MAWoodMain/esp-powermonitor/main/wifi.c

//
// Created by MattWood on 21/07/2021.
//

/**************************** LIB INCLUDES ******************************/
/**************************** USER INCLUDES *****************************/
#include "wifi.h"
#include "esp_wifi.h"
#include "esp_event.h"
#include "config.h"
/******************************* DEFINES ********************************/
#define WIFI_CONNECTED_BIT BIT0
#define WIFI_FAIL_BIT      BIT1
/***************************** STRUCTURES *******************************/
/************************** FUNCTION PROTOTYPES *************************/
static void wifi_event_handler(void* arg, esp_event_base_t event_base,
                               int32_t event_id, void* event_data);
/******************************* CONSTANTS ******************************/
static const char *TAG = "WIFI";
/******************************* VARIABLES ******************************/
static EventGroupHandle_t wifi_event_group;
static int wifi_retry_num = 0;
/*************************** PUBLIC FUNCTIONS ***************************/

bool wifi_init(void)
{
    wifi_event_group = xEventGroupCreate();


    ESP_ERROR_CHECK(esp_netif_init());

    ESP_ERROR_CHECK(esp_event_loop_create_default());
    esp_netif_create_default_wifi_sta();

    wifi_init_config_t cfg = WIFI_INIT_CONFIG_DEFAULT();
    ESP_ERROR_CHECK(esp_wifi_init(&cfg));

    esp_event_handler_instance_t instance_any_id;
    esp_event_handler_instance_t instance_got_ip;
    ESP_ERROR_CHECK(esp_event_handler_instance_register(WIFI_EVENT,
                                                        ESP_EVENT_ANY_ID,
                                                        &wifi_event_handler,
                                                        NULL,
                                                        &instance_any_id));
    ESP_ERROR_CHECK(esp_event_handler_instance_register(IP_EVENT,
                                                        IP_EVENT_STA_GOT_IP,
                                                        &wifi_event_handler,
                                                        NULL,
                                                        &instance_got_ip));

    wifi_config_t wifi_config = {
            .sta = {
                    /* Setting a password implies station will connect to all security modes including WEP/WPA.
                     * However these modes are deprecated and not advisable to be used. Incase your Access point
                     * doesn't support WPA2, these mode can be enabled by commenting below line */
                    .threshold.authmode = WIFI_AUTH_WPA2_PSK,

                    .pmf_cfg = {
                            .capable = true,
                            .required = false
                    },
            },
    };
    memset(wifi_config.sta.ssid, 0, sizeof(wifi_config.sta.ssid));
    strcpy((char*)wifi_config.sta.ssid, config_getStringField(CONFIG_STRING_FIELD_WIFI_SSID));
    memset(wifi_config.sta.password, 0, sizeof(wifi_config.sta.password));
    strcpy((char*)wifi_config.sta.password, config_getStringField(CONFIG_STRING_FIELD_WIFI_PASSWORD));
    ESP_ERROR_CHECK(esp_wifi_set_mode(WIFI_MODE_STA) );
    ESP_ERROR_CHECK(esp_wifi_set_config(WIFI_IF_STA, &wifi_config) );
    /* TODO: check for errors */
    return true;
}

bool wifi_connect()
{
    return ESP_OK == esp_wifi_start();
}

bool wifi_switchToSoftAP()
{
    esp_wifi_stop();
    esp_netif_create_default_wifi_ap();
    wifi_init_config_t cfg = WIFI_INIT_CONFIG_DEFAULT();
    ESP_ERROR_CHECK(esp_wifi_init(&cfg));
    wifi_config_t wifi_config = {
            .ap = {
                    .ssid = "ESP_AP",
                    .ssid_len = strlen("ESP_AP"),
                    .channel = 1,
                    .password = "testpass",
                    .max_connection = 4,
                    .authmode = WIFI_AUTH_WPA_WPA2_PSK
            },
    };
    if (strlen("testpass") == 0) {
        wifi_config.ap.authmode = WIFI_AUTH_OPEN;
    }

    ESP_ERROR_CHECK(esp_wifi_set_mode(WIFI_MODE_AP));
    ESP_ERROR_CHECK(esp_wifi_set_config(WIFI_IF_AP, &wifi_config));
    /* TODO: check for errors */
    return true;
}

bool wifi_waitForConnection(uint32_t timeoutMs)
{
    bool retVal = false;
    EventBits_t bits = xEventGroupWaitBits(wifi_event_group,
                                           WIFI_CONNECTED_BIT | WIFI_FAIL_BIT,
                                           pdFALSE,
                                           pdFALSE,
                                           pdMS_TO_TICKS(timeoutMs));
    if (bits & WIFI_CONNECTED_BIT) {
        retVal = true;
    }

    return retVal;
}

/*************************** PRIVATE FUNCTIONS **************************/

static void wifi_event_handler(void* arg, esp_event_base_t event_base,
                              int32_t event_id, void* event_data)
{
    if (event_base == WIFI_EVENT && event_id == WIFI_EVENT_STA_START) {
        esp_wifi_connect();
    } else if (event_base == WIFI_EVENT && event_id == WIFI_EVENT_STA_DISCONNECTED) {
        if (wifi_retry_num < 3) {
            esp_wifi_connect();
            wifi_retry_num++;
            ESP_LOGI(TAG, "retry to connect to the AP");
        } else {
            xEventGroupSetBits(wifi_event_group, WIFI_FAIL_BIT);
        }
        ESP_LOGI(TAG,"connect to the AP fail");
    } else if (event_base == IP_EVENT && event_id == IP_EVENT_STA_GOT_IP) {
        ip_event_got_ip_t* event = (ip_event_got_ip_t*) event_data;
        ESP_LOGI(TAG, "got ip:" IPSTR, IP2STR(&event->ip_info.ip));
        wifi_retry_num = 0;
        xEventGroupSetBits(wifi_event_group, WIFI_CONNECTED_BIT);
    }
}
