MAWoodMain/esp-powermonitor/main/power_monitor.h

//
// Created by MattWood on 16/07/2021.
//

#ifndef POWER_MONITOR_H
#define POWER_MONITOR_H

/**************************** LIB INCLUDES ******************************/
/**************************** USER INCLUDES *****************************/

#include "std_includes.h"

/******************************* DEFINES ********************************/
/******************************** ENUMS *********************************/
/****************************** TYPEDEFS ********************************/
/***************************** STRUCTURES *******************************/
/************************** FUNCTION PROTOTYPES *************************/

bool power_monitor_init(void);

/******************************* GLOBALS ********************************/

#endif /* POWER_MONITOR_H */
